diving91/Oil-Boiler-Monitoring/Pictures/Sketch screen on Jeedom controller.png

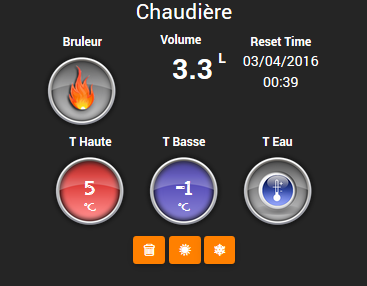
Pictures/Sketch screen on Jeedom controller.png
